wangyeee/IoTNode/iot_cfg.h

#ifndef _IOT_CFG_H_
#define _IOT_CFG_H_

#ifdef __cplusplus
extern "C" {
#endif

//#define ENABLE_SPI2SERIAL /* used for nrf24l01 to PC bridge, all nodelink listeners will be disabled */

#ifdef __cplusplus
}
#endif
#endif /* _IOT_CFG_H_ */
